SR-Wiki/COMET/Pipeline for analysis/slanCM/_1.png

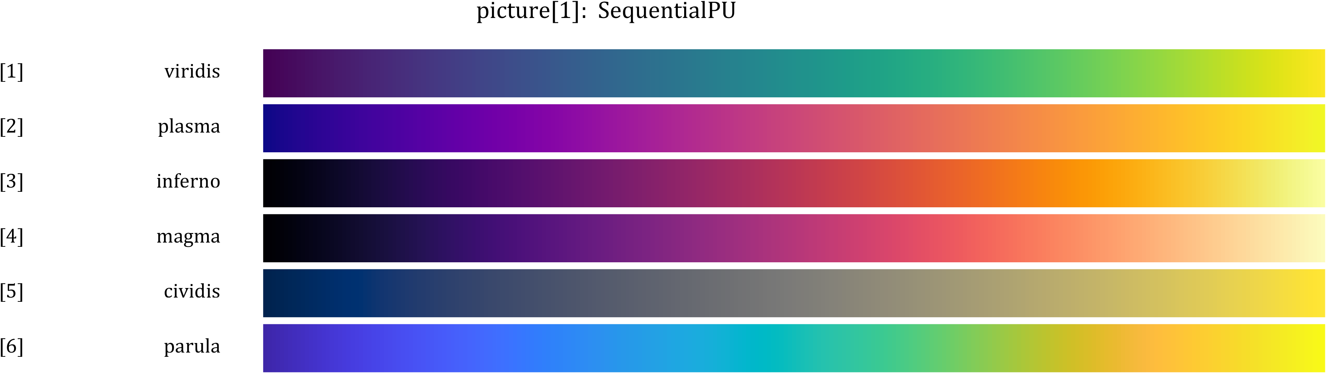
Pipeline for analysis/slanCM/_1.png
