SR-Wiki/COMET/Pipeline for analysis/slanCM/_2.png

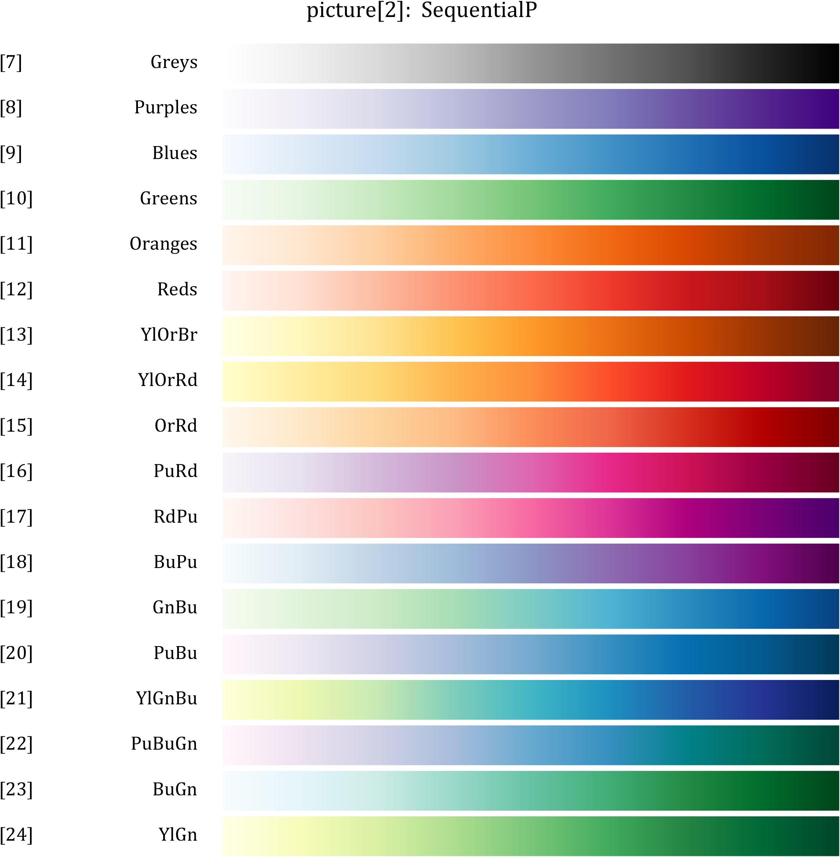
Pipeline for analysis/slanCM/_2.png
