SR-Wiki/COMET/Pipeline for analysis/slanCM/_3.png

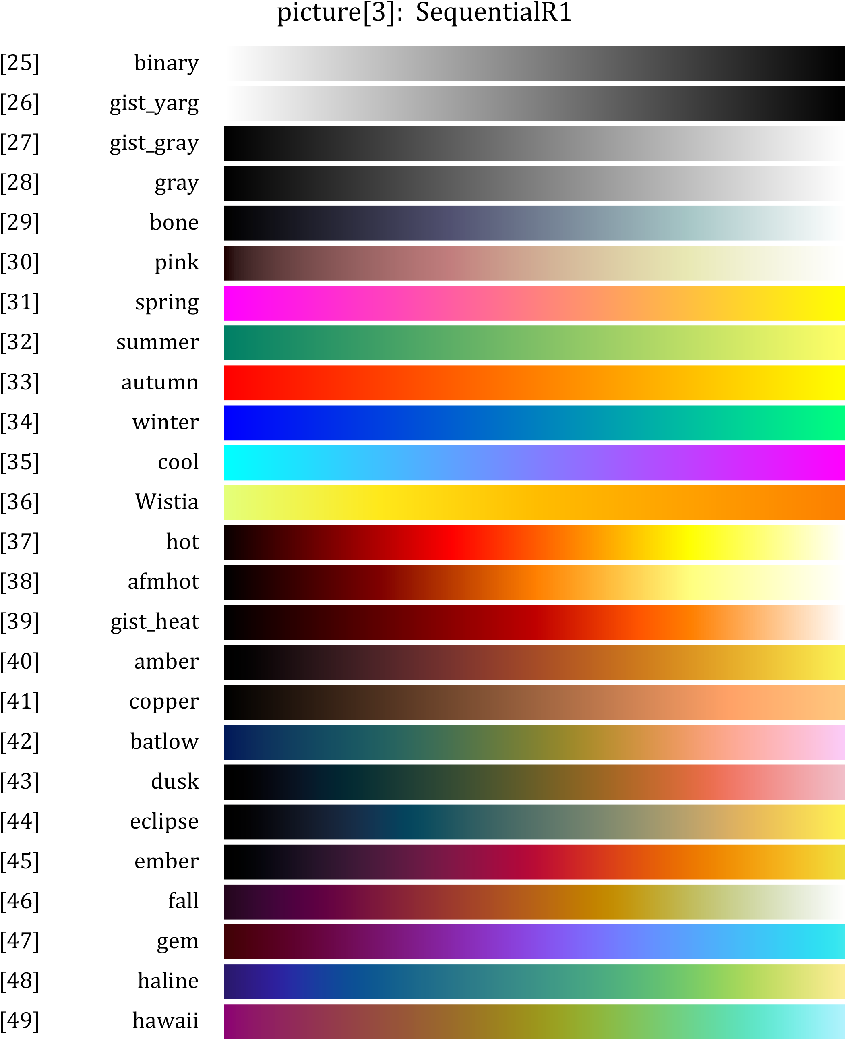
Pipeline for analysis/slanCM/_3.png
