SR-Wiki/COMET/Pipeline for analysis/slanCM/_4.png

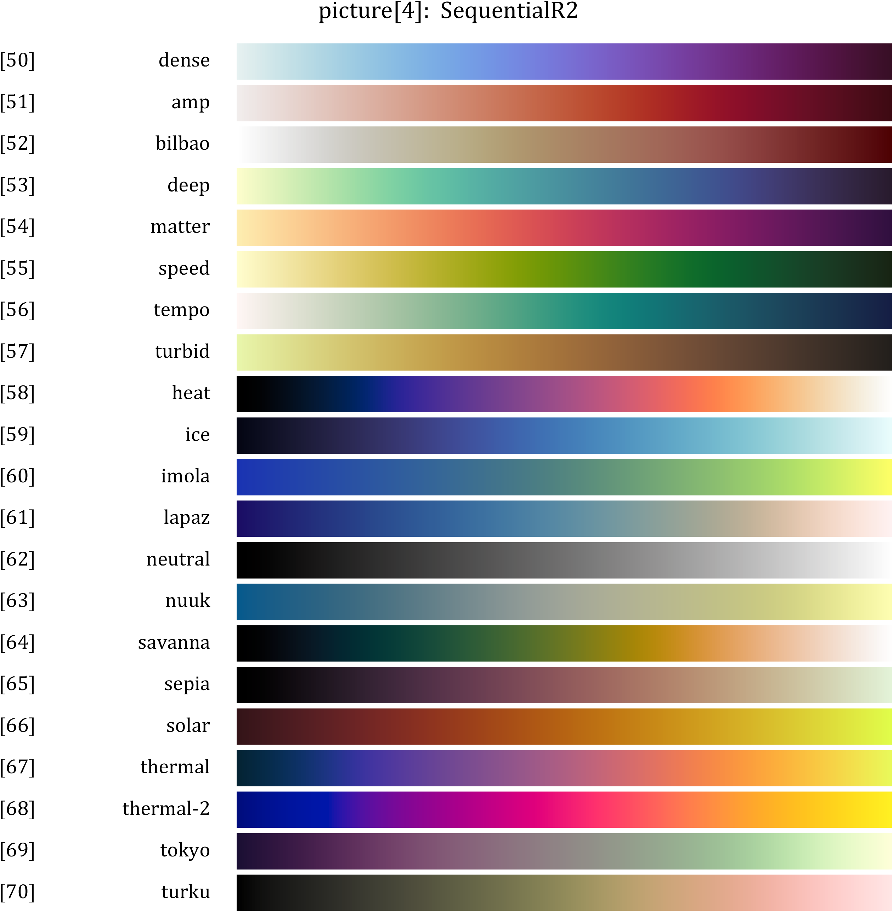
Pipeline for analysis/slanCM/_4.png
