SR-Wiki/COMET/Pipeline for analysis/slanCM/_5.png

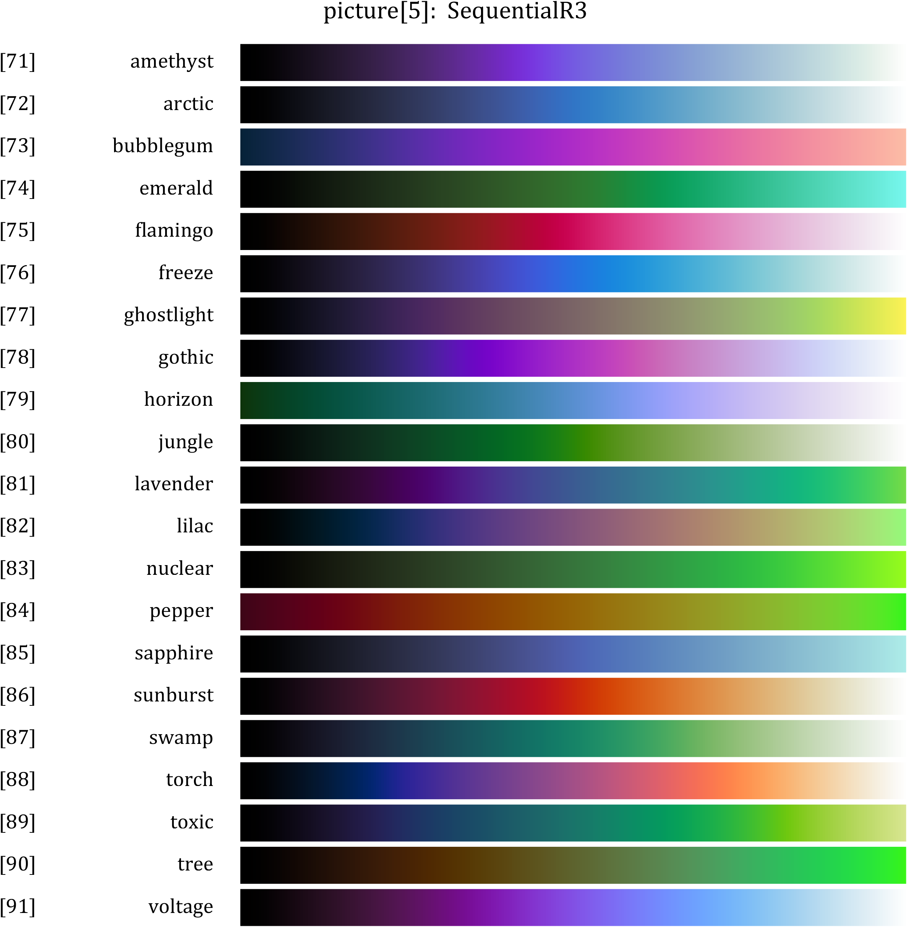
Pipeline for analysis/slanCM/_5.png
