SR-Wiki/COMET/Pipeline for analysis/slanCM/_6.png

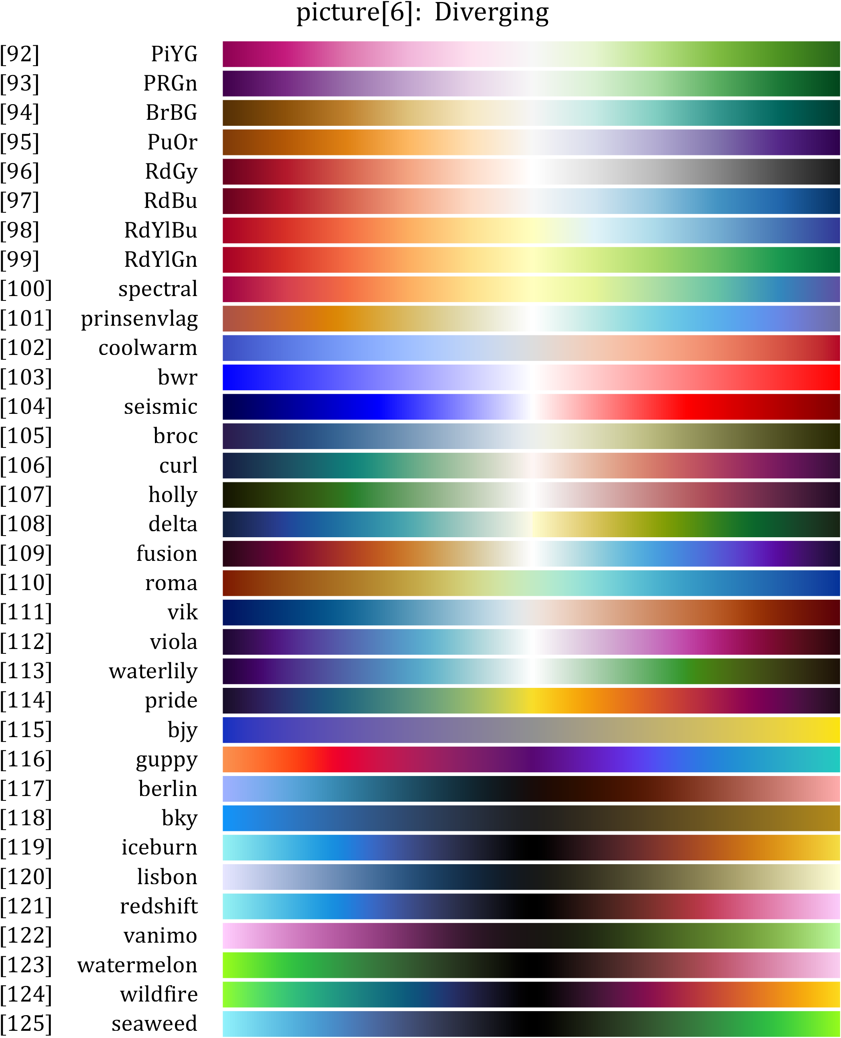
Pipeline for analysis/slanCM/_6.png
