SR-Wiki/COMET/Pipeline for analysis/slanCM/_7.png

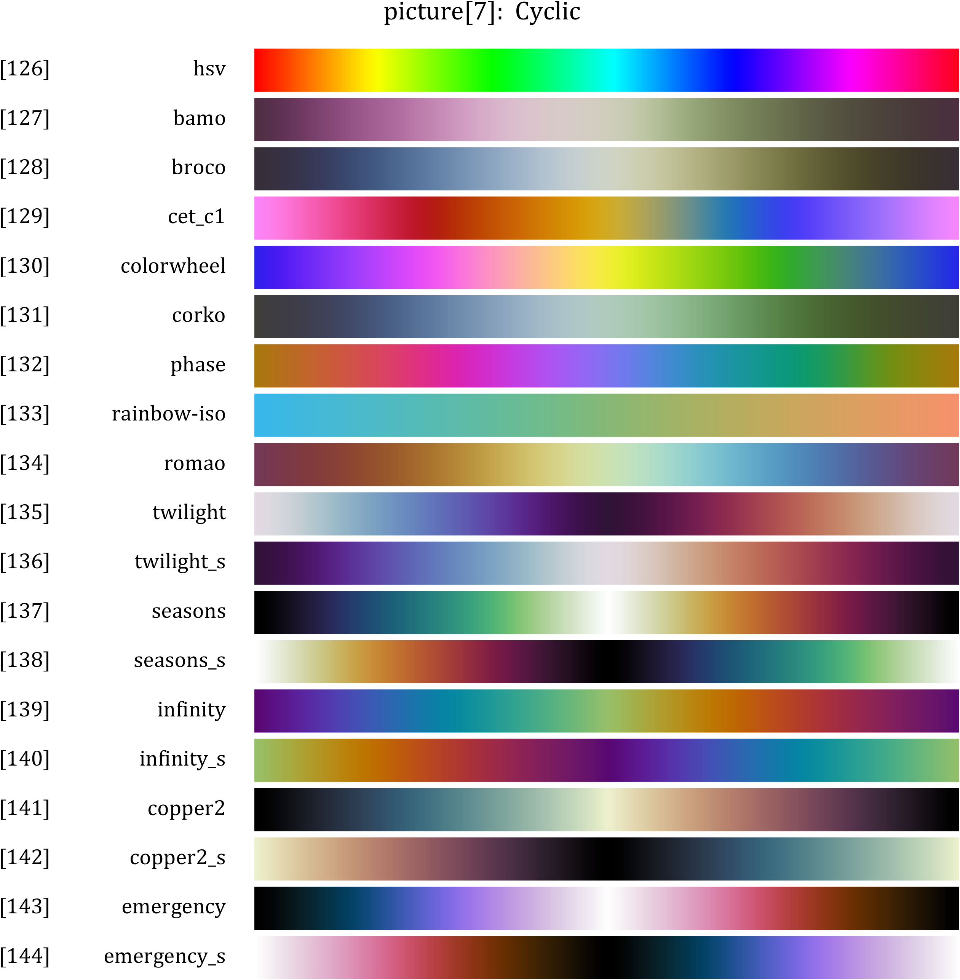
Pipeline for analysis/slanCM/_7.png
