SR-Wiki/COMET/Pipeline for analysis/slanCM/_8.png

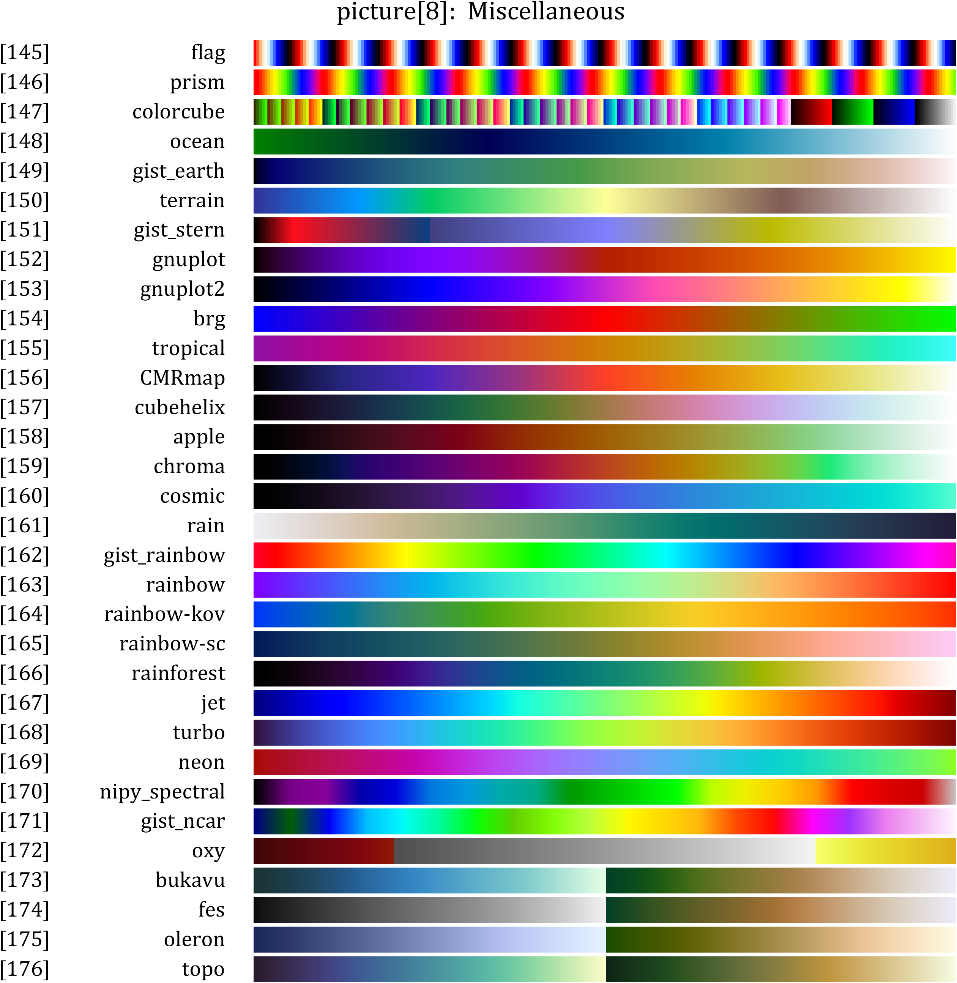
Pipeline for analysis/slanCM/_8.png
