SR-Wiki/COMET/Pipeline for analysis/slanCM/_9.png

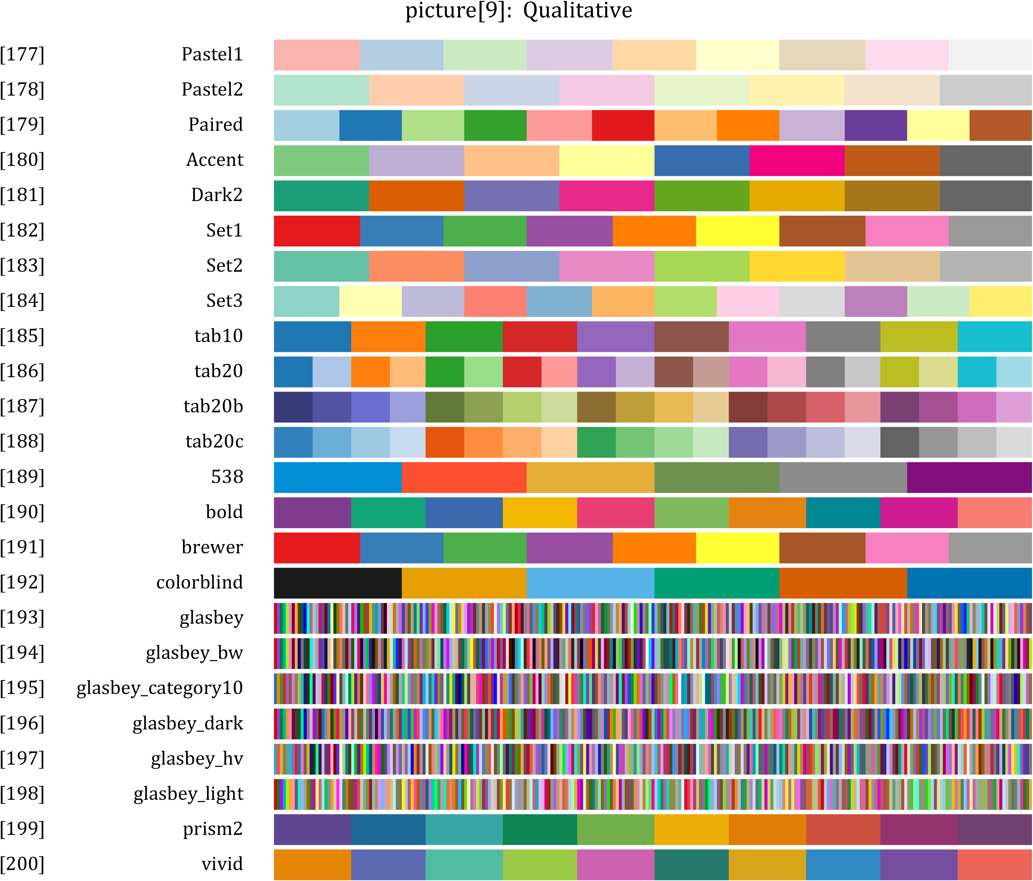
Pipeline for analysis/slanCM/_9.png
