SR-Wiki/COMET/Pipeline for analysis/slanCM/_demo1.png

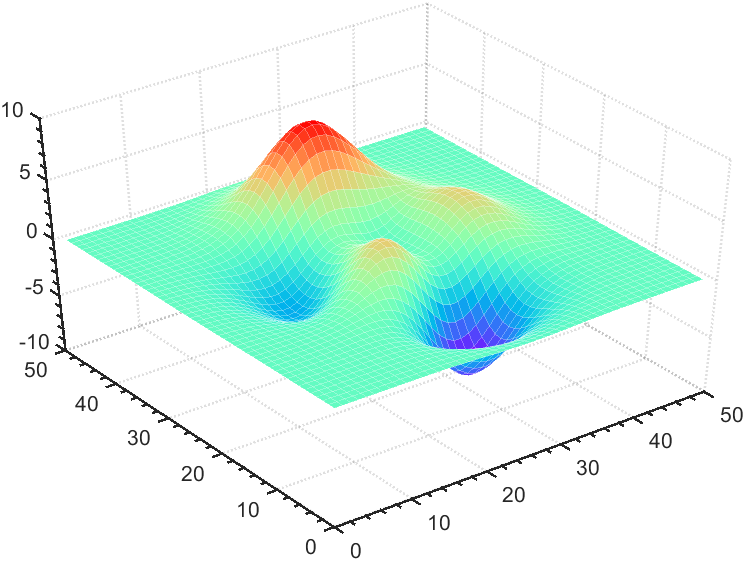
Pipeline for analysis/slanCM/_demo1.png
