SR-Wiki/COMET/Pipeline for analysis/slanCM/_demo2.png

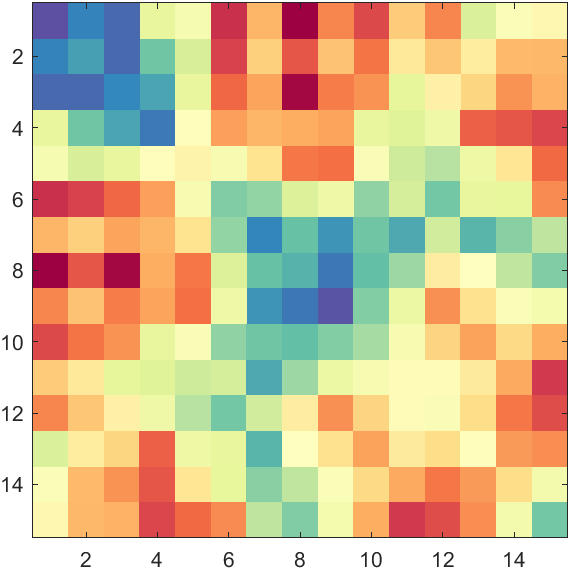
Pipeline for analysis/slanCM/_demo2.png
