SR-Wiki/COMET/Pipeline for analysis/slanCM/_demo3.png

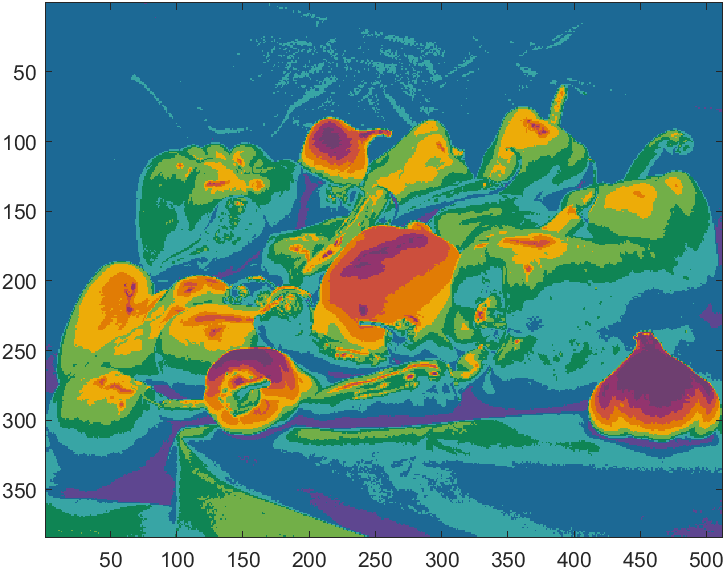
Pipeline for analysis/slanCM/_demo3.png
