SR-Wiki/COMET/Pipeline for analysis/slanCM/_demo4_1.png

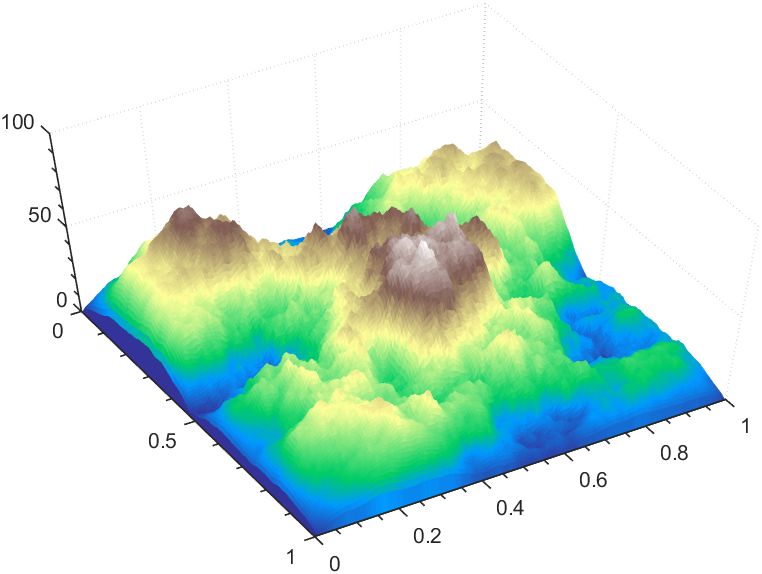
Pipeline for analysis/slanCM/_demo4_1.png
