SR-Wiki/COMET/Pipeline for analysis/slanCM/_demo4_2.png

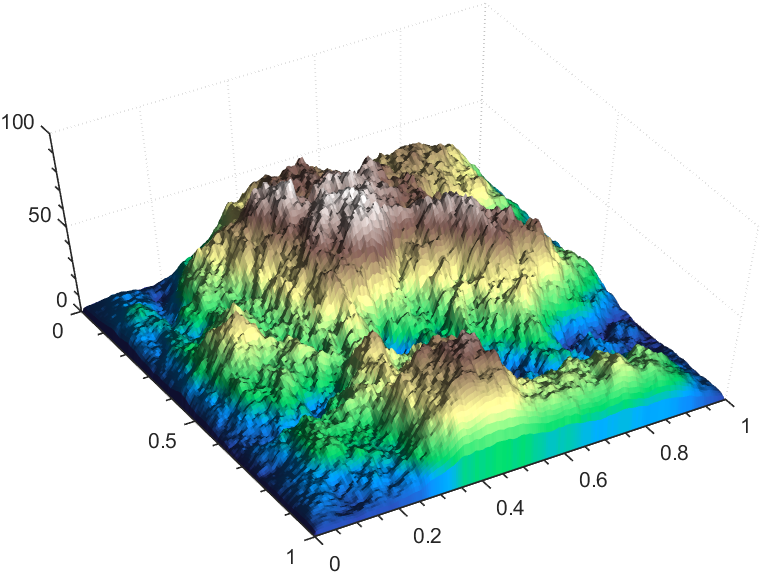
Pipeline for analysis/slanCM/_demo4_2.png
