SR-Wiki/COMET/Pipeline for analysis/slanCM/_demo5_1.png

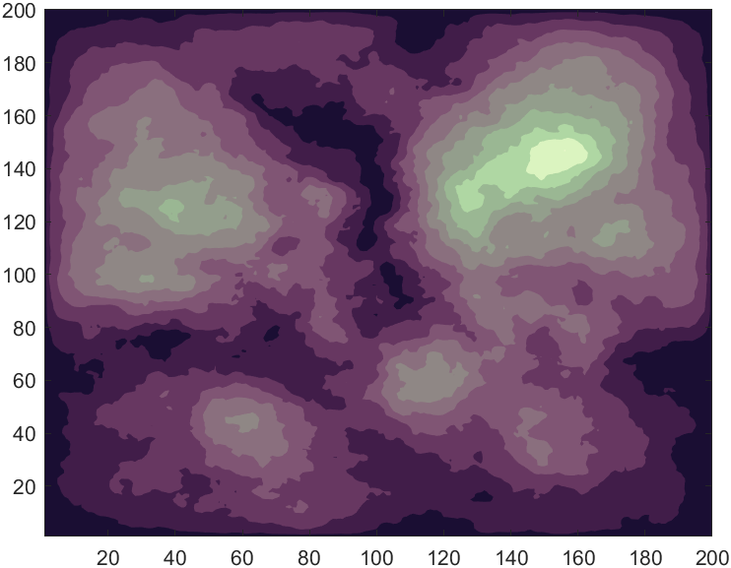
Pipeline for analysis/slanCM/_demo5_1.png
