SR-Wiki/COMET/Pipeline for analysis/slanCM/_demo5_2.png

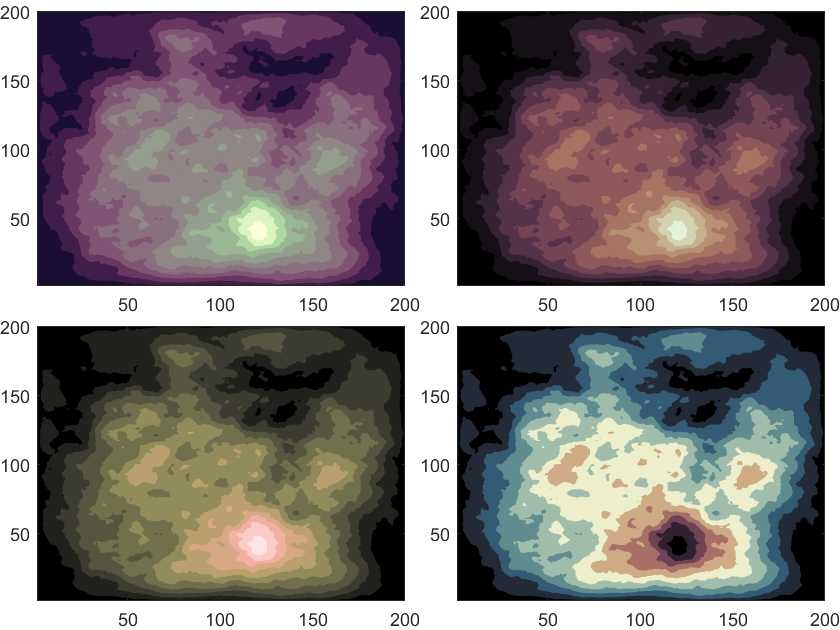
Pipeline for analysis/slanCM/_demo5_2.png
