SR-Wiki/COMET/Pipeline for analysis/slanCM/_demo6.png

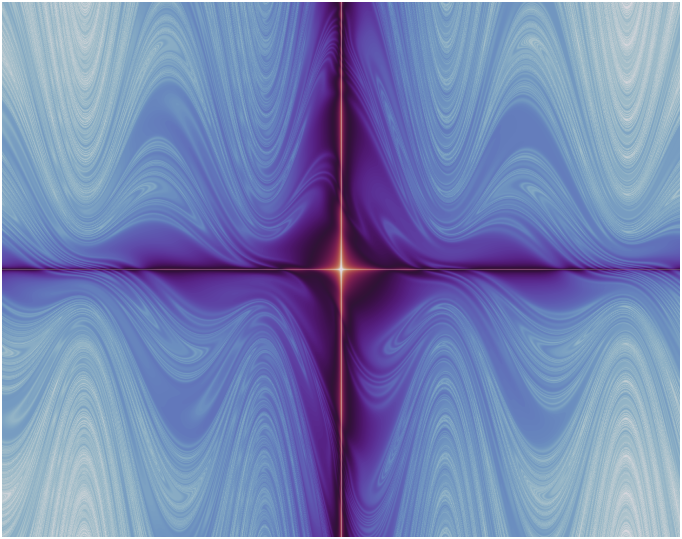
Pipeline for analysis/slanCM/_demo6.png
