SR-Wiki/COMET/Pipeline for analysis/slanCM/_demo7.png

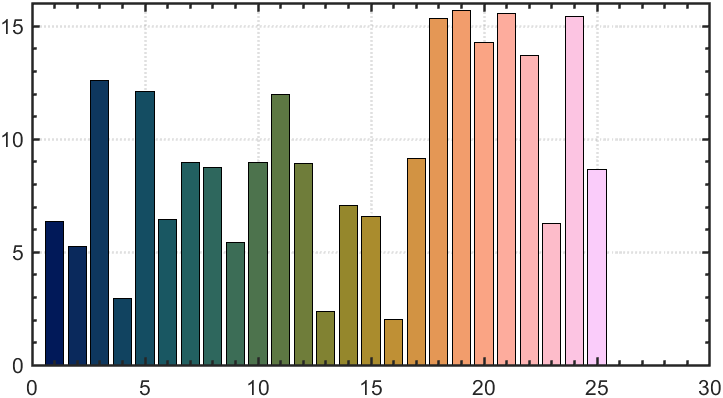
Pipeline for analysis/slanCM/_demo7.png
