SR-Wiki/COMET/Pipeline for analysis/slanCM/_demo7_2.png

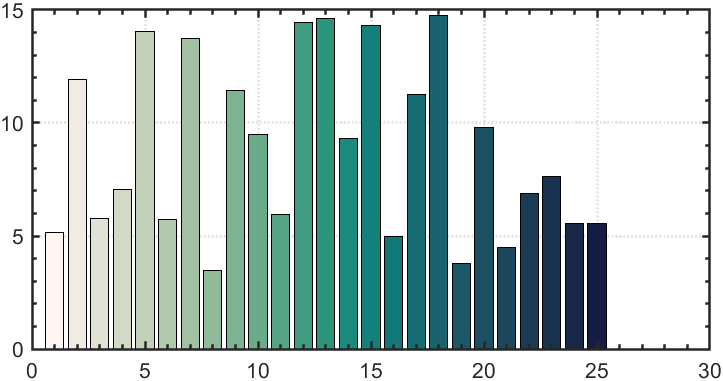
Pipeline for analysis/slanCM/_demo7_2.png
