SR-Wiki/COMET/Pipeline for analysis/slanCM/_demo7_3.png

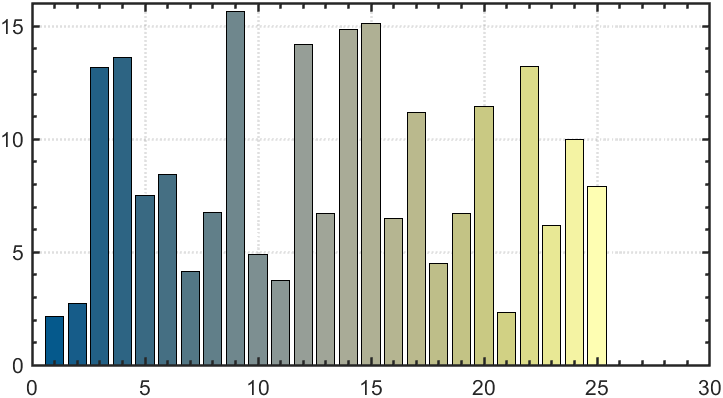
Pipeline for analysis/slanCM/_demo7_3.png
