SR-Wiki/COMET/Pipeline for analysis/slanCM/_demo7_4.png

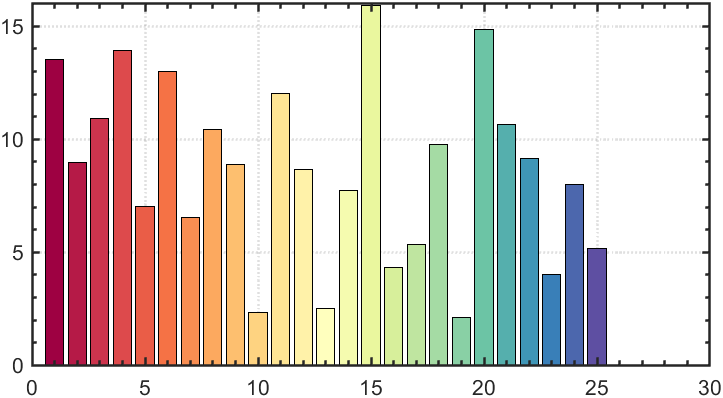
Pipeline for analysis/slanCM/_demo7_4.png
