SR-Wiki/COMET/Pipeline for analysis/slanCM/_demo7_5.png

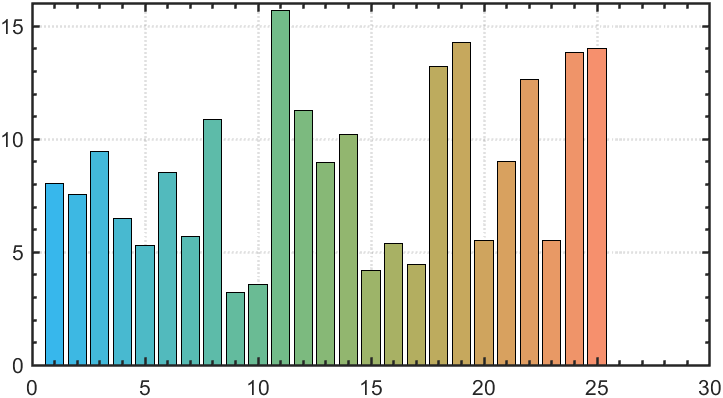
Pipeline for analysis/slanCM/_demo7_5.png
