SR-Wiki/COMET/Pipeline for analysis/slanCM/_demo7_6.png

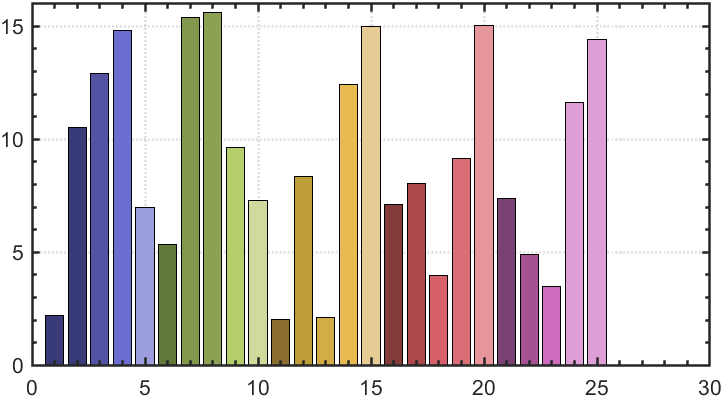
Pipeline for analysis/slanCM/_demo7_6.png
