SR-Wiki/COMET/Pipeline for analysis/slanCM/_demo8.png

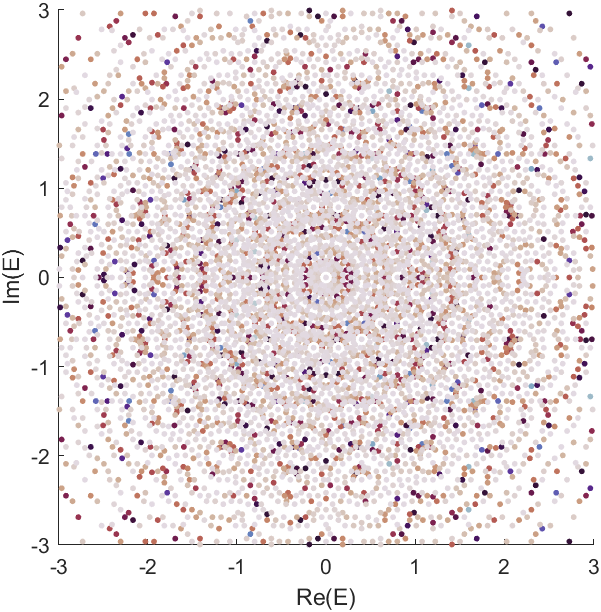
Pipeline for analysis/slanCM/_demo8.png
