SR-Wiki/COMET/Pipeline for analysis/slanCM/_demo9_1.png

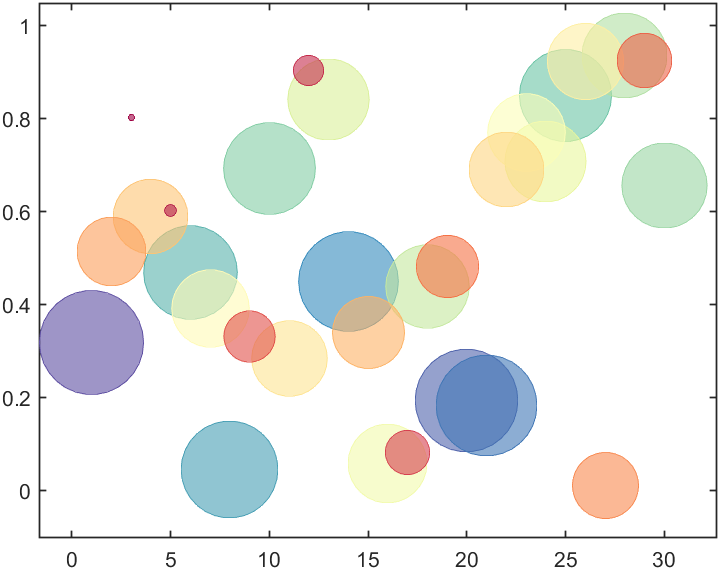
Pipeline for analysis/slanCM/_demo9_1.png
