SR-Wiki/COMET/Pipeline for analysis/slanCM/_demo9_2.png

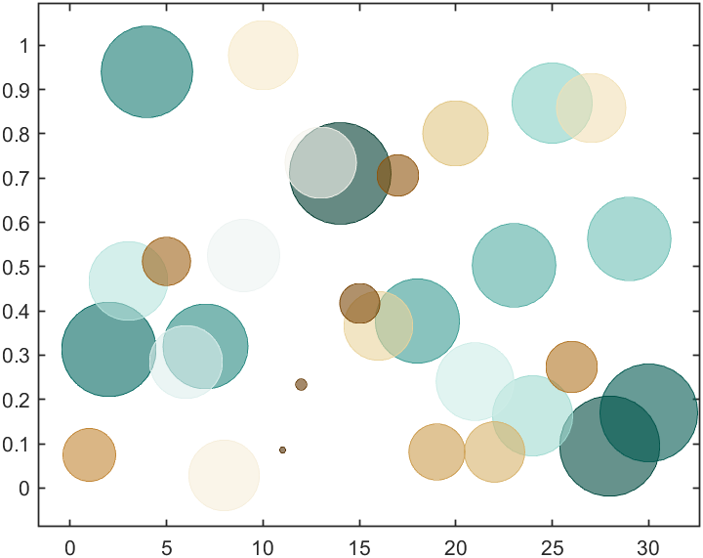
Pipeline for analysis/slanCM/_demo9_2.png
