SR-Wiki/COMET/Pipeline for analysis/slanCM/_demo9_3.png

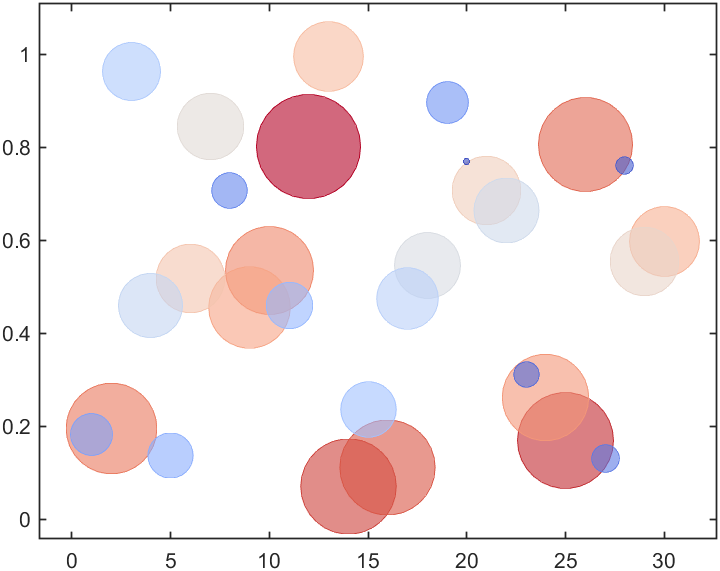
Pipeline for analysis/slanCM/_demo9_3.png
