SR-Wiki/COMET/Pipeline for image processing/SN2N/imgs/4color-small.gif

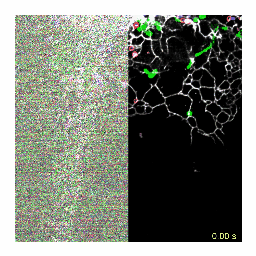
Pipeline for image processing/SN2N/imgs/4color-small.gif
