SR-Wiki/COMET/UCLA Miniscope-DAQ-QT-Software/Miniscope-DAQ-QT-Software/QtQuick/Controls/Styles/Base/images/spinner_large.png

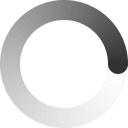
UCLA Miniscope-DAQ-QT-Software/Miniscope-DAQ-QT-Software/QtQuick/Controls/Styles/Base/images/spinner_large.png
