SR-Wiki/COMET/UCLA Miniscope-DAQ-QT-Software/wikiImg/Example_Main_Window.PNG

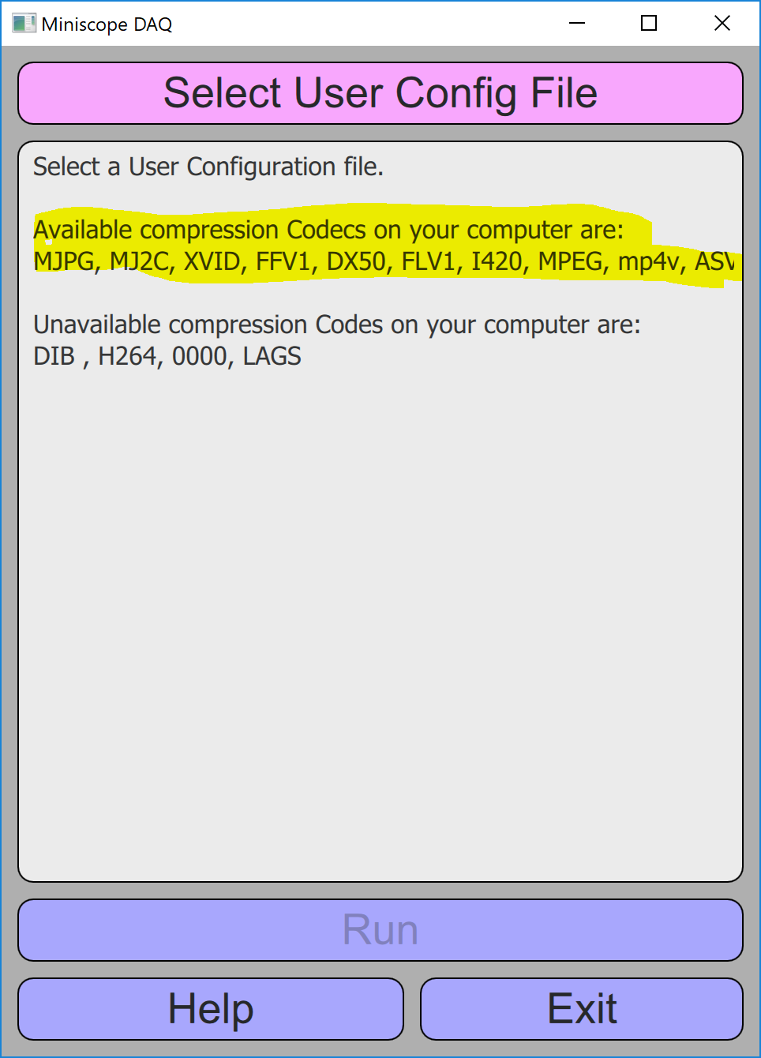
UCLA Miniscope-DAQ-QT-Software/wikiImg/Example_Main_Window.PNG
