SR-Wiki/COMET/UCLA Miniscope-DAQ-QT-Software/wikiImg/gif/Miniscope_Window.gif

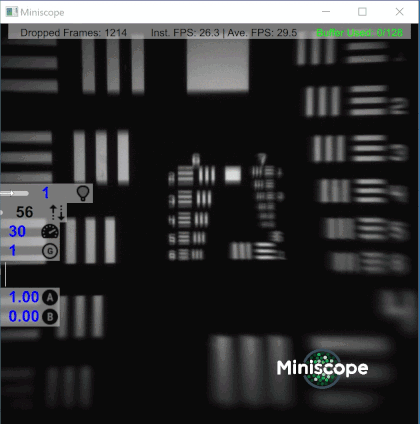
UCLA Miniscope-DAQ-QT-Software/wikiImg/gif/Miniscope_Window.gif
