SR-Wiki/COMET/UCLA Miniscope-DAQ-QT-Software/wikiImg/gif/Open_Software.gif

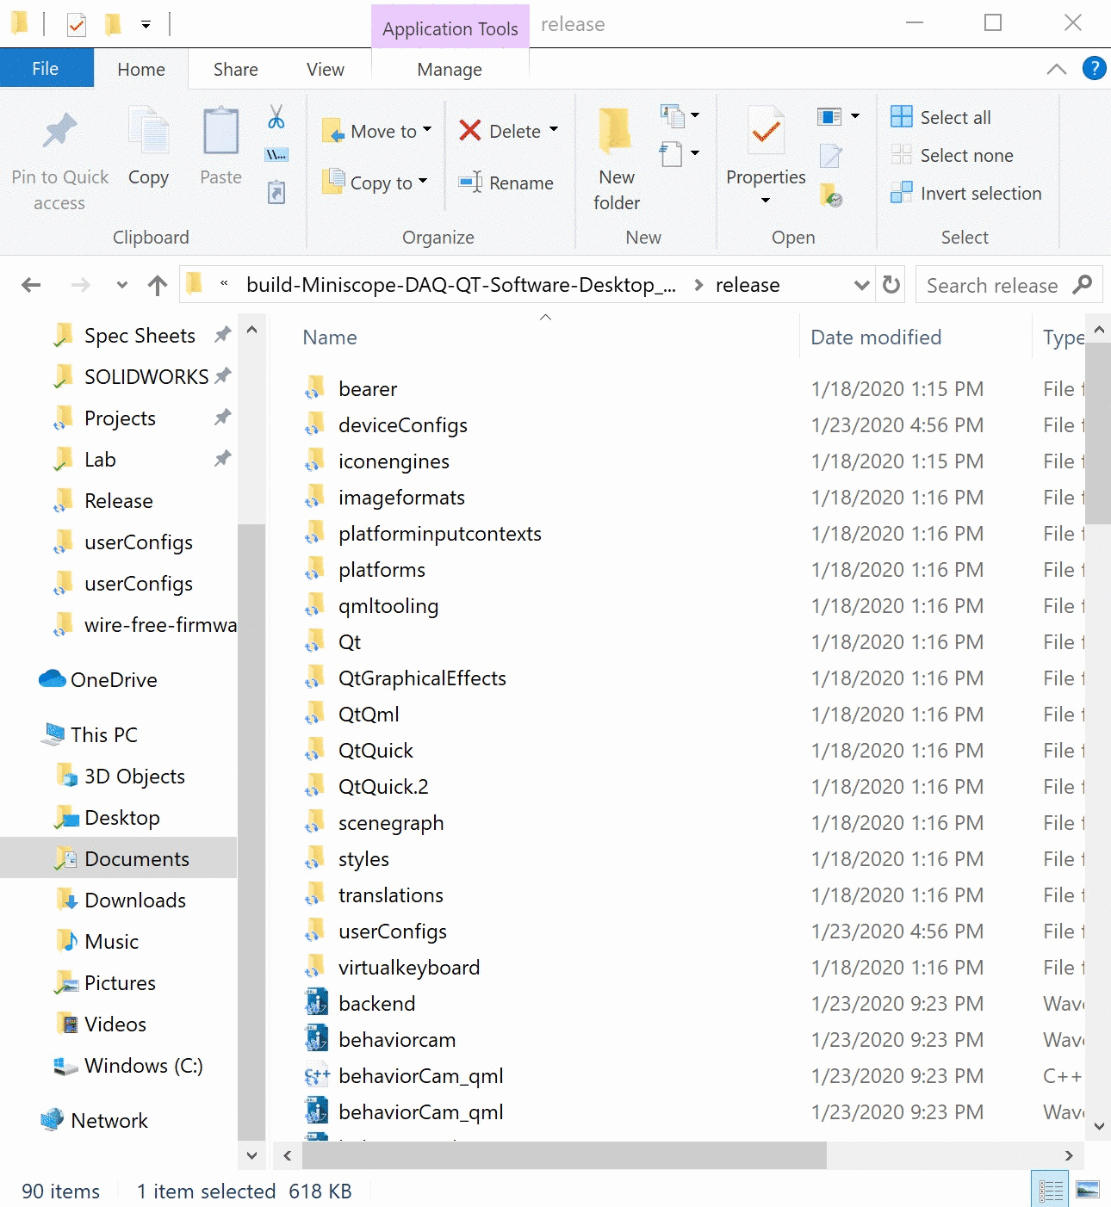
UCLA Miniscope-DAQ-QT-Software/wikiImg/gif/Open_Software.gif
