SR-Wiki/COMET/UCLA Miniscope-DAQ-QT-Software/wikiImg/gif/Select_UserConfig.gif

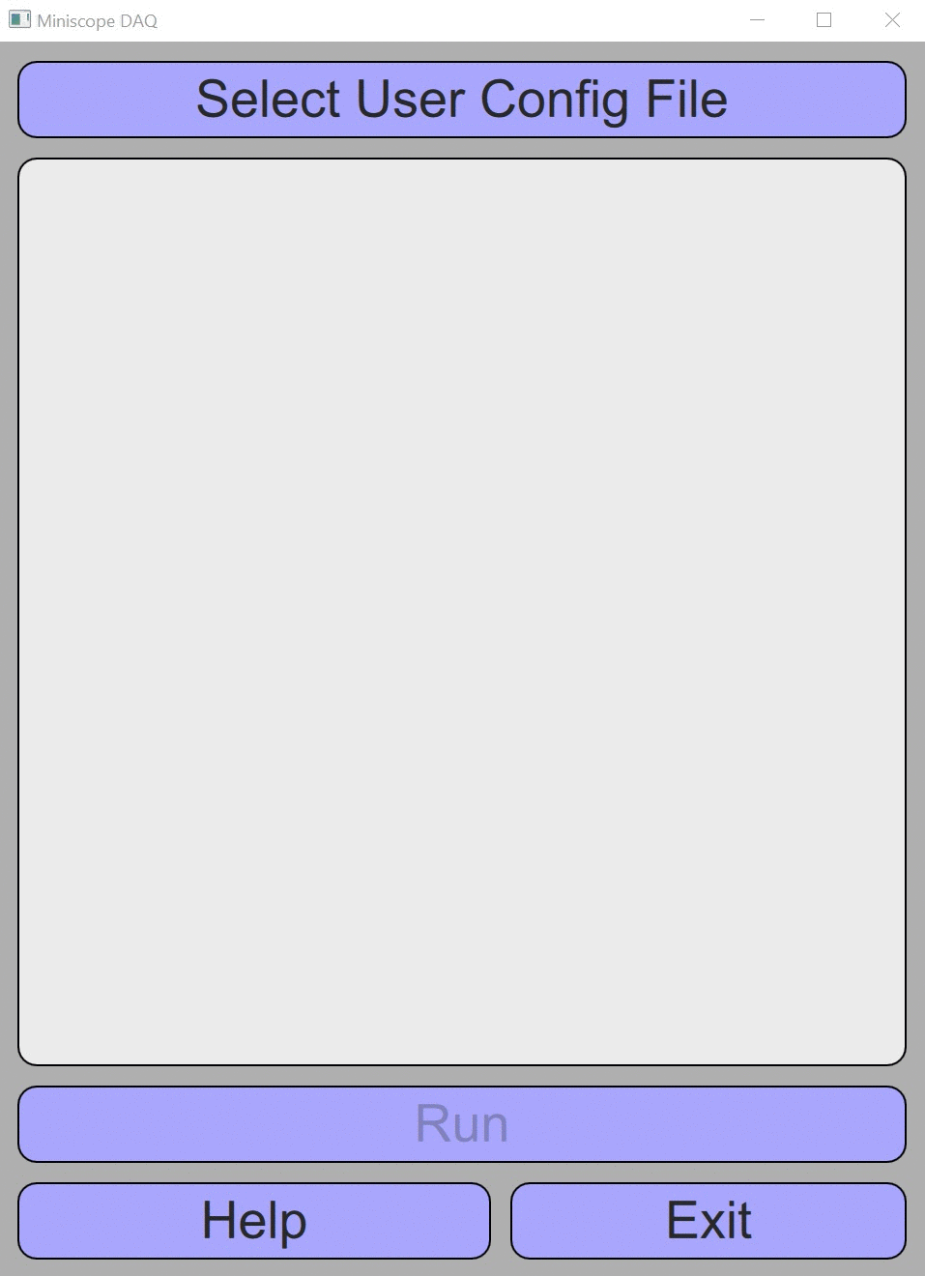
UCLA Miniscope-DAQ-QT-Software/wikiImg/gif/Select_UserConfig.gif
