SR-Wiki/COMET/UCLA Miniscope-DAQ-QT-Software/wikiImg/miniscope_bright.png

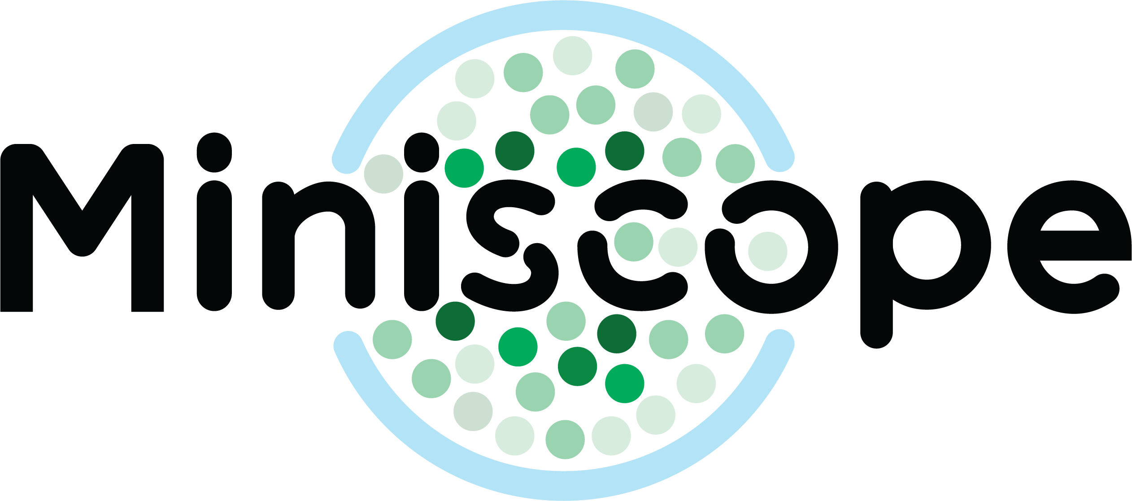
UCLA Miniscope-DAQ-QT-Software/wikiImg/miniscope_bright.png
